aboller1212/canarynode/firmware/src/fdcan.c

#include "stm32g474xx.h"
#include <stdint.h>
#include "fdcan.h"

void fdcan_init(void) {
    // --- GPIOA Enable ---
    //Enable the GPIOA clock, sets the GPIOA bit high without changing other bit configurations
    RCC->AHB2ENR |= RCC_AHB2ENR_GPIOAEN;

    // --- clock ---
    //enables the register access clock on APB1 (like every peripherhal so we can read/write its perihpherals)
    RCC->APB1ENR1 |= RCC_APB1ENR1_FDCANEN;
    //enables the kernel clock that drives the CAN bit timing
    //we need FDCANSEL -> 10 = PCLK1(clock delivered to perhipherals on the APB1 bus)
    RCC->CCIPR &= ~RCC_CCIPR_FDCANSEL; //clears the 2 bits to 0
    RCC->CCIPR |= RCC_CCIPR_FDCANSEL_1; //sets to 10 = PCLK1 (16MHz Clock)


    // --- PINS: PA11 = FDCAN1_RX, PA12 = FDCAN1_TX, both AF9
    /*
        10 = alternate function, PA11 field is MODE11, PA12 field is MODE12, set 10 to both
        AFR = Alternate Function Register, AFR[1] is used for pins 8-15, AFR[0] for 0-7
        position of pin N's field in AFR[1] = (N-8) *4
        (11-8)*4 = bit 12 field [15:12] -PA11-> AF9 = FDCAN1_RX
        (12-8)*4 = bit 16 field [19:16] -PA12->AF9 = FDCAN_TX
        //Note: each pins AFR field is 4 bits
    */
    GPIOA->MODER &= ~(GPIO_MODER_MODE11 | GPIO_MODER_MODE12); //clear both fields
    GPIOA->MODER |= (GPIO_MODER_MODE11_1 | GPIO_MODER_MODE12_1); //set bit 1 to each of the fields so 10 is in both mode11 and mode12

    //0xFu <<12 = the 4-bit mask for PA11s AF field (clear all 4 bits), same for 0xFu <<16 for PA12s
    GPIOA->AFR[1] &= ~((0xFu << 12) | (0xFu <<16)); //clear both 4-bit AF fields
    GPIOA->AFR[1] |= ((9u << 12) | (9u << 16)); //set both fields to AF9(FDCAN1)

    // --- enter init mode ---
    /*
        PCLK1: 16MHz peripheral clock on APB1 -> set the kernel to use this clock
        bit rate: bits per second on the bus: I use 500 kbit/s as a standard CAN rate
        Tq: (time quantum) the smallest time slice of a bit | 16MHz / 500 kbit | 1 bit = 32 Tq
        -> prescaler: divides the kernel clock to set how long one Tq is
        -> prescaler = 1 | Tq = prescaler / kernel_clock = 1/16Hz = 62.5ns = 1 Tq
        SYNC: the fixed 1 Tq slot at the start of each bit (node clock realignment)
        Tseg1: The chunk of Tq from SYNC up to the sample point
        Tseg2: The chunk of Tq from the sample point to the bits end
        -> Want to read at ~80% for the sample point (don't want to take too early)
        -> SYNC(1) + Tseg1 + Tseg2 = 32 | Tseg1 + Tseg2 = 31
        -> (1 + Tseg1) / 32 = 0.80 | Tseg1 = 25 -> Tseg2 = 6 -> 26/32 = 81.3%
    */
    //CCCR: FDCANs main control register
    //FDCAN_CCCR_INIT = Initialization bit
    //FDCAN_CCCR_CCE = Configuration Change Enable
    FDCAN1->CCCR |= FDCAN_CCCR_INIT; //request init mode
    //Blocking-busy wait: fine for one-time setup
    while(!(FDCAN1->CCCR & FDCAN_CCCR_INIT)); // & checks only the init bit in the CCCR register, loops until its set
    FDCAN1->CCCR |= FDCAN_CCCR_CCE; // config change enable, unlocks NBTP

    // --- bit timing (500 kbit/s) ---
    // (=) we are writing the whole register : (|) packs all four into one 32-bit word
    //from RMOS: bit time = (1 + (NTSEG1+1) + (NTSEG2+1)) × (NBRP+1) so thats why we subtract 1 going in
    //each xu is unsigned number x being stored in their respective areas for the NBTP register
    FDCAN1->NBTP = (0u << FDCAN_NBTP_NSJW_Pos) //SJW = 1 -> 0
                | (0u << FDCAN_NBTP_NBRP_Pos) //prescaler = 1 -> 0
                | (24u << FDCAN_NBTP_NTSEG1_Pos) //Tseg1 = 25 -> 24
                | (5u << FDCAN_NBTP_NTSEG2_Pos); //Tseg2 = 6 -> 5

    // --- accept all frames into FIFO 0 ---
    /*
        CAN needs a dedicated spot in RAM because CAN-FD messages can be 64-bits of data
        this is a lot so FDCAN will put the data in a small RAM areas and I congfig registers to divide the RAM
        Filter list: which incoming IDs do I accept?
        Rx FIFO 0: incoming messages land here (N slots)
        ^ Note: FDCAN has two receive inboxes FIFO0 and FIFO1, They're seperate queues in the message RAM, so you can route traffic to different inboxes 
        Tx buffers: outgoing messages I write here (M slots)
        To transmit: write message (ID+data) into a Tx buffer slot in the RAM, then poke register TXBAR telling it to send buffer
        To receive: FDCAN puts the messages into the Rx FIFO area, we read status register RXFOS to see how many are waiting and to read out of RAM
    */

    // RXGFC = RX Global Filter Configuration : controls FDCAN's global rule for what happens to incoming frames
    // ^ normally a node sets up filters, a list of IDs it cares about, either frames match a filter or don't
    // ANFS = Accept Non-matching Frames, Standard, bit 4 : no filter->00 = put it in Rx FIFO 0 (01 = FIFO 1, 10/11 = reject)
    // ^ 2 bit field in RXGFC (RMO0440). 00=accept Rx in FIFO 0, 01=accept Rx in FIFO 1, 10/11 = reject
    // LSS = List Size Standard, bit 16 : how many standard filters you've defined -> I've set 0
    
    //Sets the values in the RXGFC register for LSS and ANFS, the other fields just get their reset values
    FDCAN1->RXGFC = (0u << FDCAN_RXGFC_LSS_Pos) //there are 0 standard filters
                | (0u << FDCAN_RXGFC_ANFS_Pos); //non-matching std frames -> Rx FIFO 0

    // --- loopback (comment these out for the real bus) ---
    //Internal loopback (self-test, no pins or bus)
    FDCAN1->CCCR |= FDCAN_CCCR_TEST; // enable test mode (unlocks the TEST register)
    FDCAN1->CCCR |= FDCAN_CCCR_MON; // bus monitoring -> maked loopback INTERNAL : MON = TX loops to RX inside the chip, pins disconnected
    FDCAN1->TEST |= FDCAN_TEST_LBCK; // turn loopback on

    // --- leave init mode -> go live ---
    //Note: you can only change FDCANs config if INIT=1 but FDCAN will be stopped
    FDCAN1->CCCR &= ~FDCAN_CCCR_INIT; //leave init mode, FDCAN goes live (clears just the init bits)
    while(FDCAN1->CCCR & FDCAN_CCCR_INIT); //wait until FDCAN is running, use this because INIT may still read 1 for a moment after I write 0, exits once 0
}

void fdcan_send(uint32_t id, uint32_t d0, uint32_t d1) {
    //Tx buffer lives in RAM at SRAMCAN_BASE + 0x278 : this is where we write messages into this peice of memory
    //FDCAN1 Tx buffer 0 in message RAM, volatile because it can change, points to 32-bit words
    volatile uint32_t *txbuf = (volatile uint32_t *)(SRAMCAN_BASE + 0x278);
    
    //NOTE: FDCAN HARDWARE will read the 1st word as ID, 2nd word as DLC, 3+ word as data
    //The ID is in the 0 position of txbuf
    //we left-align the bits because ID slot is 29 bits, our ID field is 11-bits -> insert at bit 18, flags are 29-31(untouched)
    txbuf[0] = (id << 18); //send a message with ID 0x123
    
    //the length = 8 data bytes = dlc
    txbuf[1] = (8u << 16); //placed at the 16th bit

    //the data slots, DLC tells hardware HOW FAR TO READ, DLC = 8 = 2 bytes, reads txbuf[2,3]
    txbuf[2] = d0; //data bytes 0-3 (4 bytes per word = 32-bit)
    txbuf[3] = d1; //data bytes 4-7 
    
    //Each bit = one Tx buffer, bit0 = buffer0
    //set only register - after writing 1, the bit auto-clears
    FDCAN1->TXBAR = (1u << 0); //reguest transmission of TX buffer 0
}

void fdcan_recv(uint32_t *id, uint32_t *dlc, uint32_t *d0, uint32_t *d1) {
    //confirm the frame arrived
    //RXF0S = Rx FIFO0 status register -> Field F0FL = fill level = how many messages sitting in FIFO0 right now
    while(!(FDCAN1->RXF0S & FDCAN_RXF0S_F0FL_Msk)); //wait until a message comes, F0FL field will be greater than 0

    //Once we know that there IS a message waiting in the buffer we need to knw which of FIFO0s 3 slot hold it
    //the F0GI slot = Get Index, which FIF0 slot 0,1,2 holds the oldest unread message
    // when we do >>F0GI_Po = (>> 8) we are shifting it down to where the F0GI exists which is bit 8
    // shifting it right by 8 turns it into either 0,1,2
    uint32_t getidx = (FDCAN1->RXF0S & FDCAN_RXF0S_F0GI_Msk) >> FDCAN_RXF0S_F0GI_Pos;

    //now we need to compute the slot's address in message RAM
    // 0xB0: Rx FIFO 0s base offset in message RAM
    //getidx * 0x48 = skip to the right slot, each slot is 0x48 so getidx * 0x48 would get you to the right slot
    volatile uint32_t *rxbuf = (volatile uint32_t *)(SRAMCAN_BASE + 0xB0 + getidx * 0x48);
    //R0 = ID word, R1= DLC + Length, R2,3 = data -> same packing as Tx

    // --- write INTO the callers variable ---
    //we shift the ID field down out of [28:18], then mask 11-bits 0x7FF = 11 ones, to drop the flags
    *id = (rxbuf[0] >> 18) & 0x7FFu; 
    //Shift the dlc down from [19:16], mask 4-bits 0xF
    *dlc = (rxbuf[1] >> 16) & 0xFu; 
    //the data we sent
    *d0 = rxbuf[2]; //data bytes 0-3
    *d1 = rxbuf[3]; //data bytes 4-7

    //RXF0A = Rx FIFO 0 Acknowledghe register at FDCAN1 + 0x094
    //Field F0AI: Acknowledge index, write the slot index you just read, FDCAN advances read and frees the slot
    //no need to shift because F0AI is at [2:0] so already at the bottom
    FDCAN1->RXF0A = getidx; //acknowledge and free the slot, F0FL will drop by 1
}
